Botond24/game_console/src/game/include/game.h

#ifndef GAME_H
#define GAME_H

#include <stdint.h>
#include <stdbool.h>

struct KeyState {
    bool up;
    bool down;
    bool left;
    bool right;
    bool a;
    bool b;
};

struct HAL {
    void (*draw_pixel)(int x, int y, uint16_t color);
    void (*clear_screen)(void);
    void (*render)(void);
    KeyState (*read_input)(void);
    void (*delay_ms)(uint32_t ms);
    int screen_width;
    int screen_height;
};

#endif
