Botond24/game_console/bootloader/src/periphs/oled.cpp

// IMPORTANT: MAKE SURE TO WRAP YOUR CODE IN MUTEXES
// IF UR ACCESSING THE OLED
#include "oled.h"
#include "pins.h"
#include <Adafruit_GFX.h>
#include <Adafruit_SSD1306.h>
#include <Wire.h>

#define WIDTH 128
#define HEIGHT 64
#define OLED_I2C_ADDR 0x3C

Oled::Oled() : display(WIDTH, HEIGHT, &Wire, -1) {}

const unsigned char chippy[] PROGMEM = {
    0x00, 0x00, 0x00, 0x00, 0xff, 0xff, 0xff, 0xff, 0xff, 0xff, 0xff, 0xff,
    0x00, 0x00, 0x00, 0x00, 0x00, 0x00, 0x00, 0x01, 0xc0, 0x00, 0x00, 0x00,
    0x00, 0x00, 0x00, 0x03, 0x80, 0x00, 0x00, 0x00, 0x00, 0x00, 0x00, 0x02,
    0x00, 0x00, 0x00, 0x00, 0x00, 0x00, 0x00, 0x00, 0xc0, 0x00, 0x00, 0x00,
    0x00, 0x00, 0x00, 0x04, 0x00, 0x00, 0x00, 0x00, 0x00, 0x00, 0x00, 0x00,
    0x20, 0x00, 0x00, 0x00, 0x00, 0x00, 0x00, 0x0c, 0x00, 0x00, 0x00, 0x00,
    0x00, 0x00, 0x00, 0x00, 0x30, 0x00, 0x00, 0x00, 0x00, 0x00, 0x00, 0x08,
    0x00, 0x00, 0x00, 0x00, 0x00, 0x00, 0x00, 0x00, 0x10, 0x00, 0x00, 0x00,
    0x00, 0x00, 0x00, 0x08, 0x00, 0x00, 0x00, 0x00, 0x00, 0x00, 0x00, 0x00,
    0x10, 0x00, 0x00, 0x00, 0x00, 0x00, 0x00, 0x08, 0x00, 0x00, 0x00, 0x00,
    0x00, 0x00, 0x00, 0x00, 0x10, 0x00, 0x00, 0x00, 0x00, 0x00, 0x00, 0x08,
    0x00, 0x00, 0x00, 0x00, 0x00, 0x00, 0x00, 0x00, 0x10, 0x00, 0x00, 0x00,
    0x00, 0x00, 0x00, 0x08, 0x00, 0x00, 0x00, 0x00, 0x00, 0x00, 0x00, 0x00,
    0x10, 0x00, 0x00, 0x00, 0x00, 0x00, 0x00, 0x08, 0x00, 0x00, 0x00, 0x00,
    0x00, 0x00, 0x00, 0x00, 0x10, 0x00, 0x00, 0x00, 0x00, 0x00, 0x00, 0x08,
    0x00, 0x00, 0x00, 0x00, 0x00, 0x00, 0x00, 0x00, 0x10, 0x00, 0x00, 0x00,
    0x00, 0x00, 0x00, 0x08, 0x00, 0x00, 0x00, 0x00, 0x00, 0x00, 0x00, 0x00,
    0x10, 0x00, 0x00, 0x00, 0x00, 0x00, 0x00, 0x08, 0x00, 0x00, 0x00, 0x00,
    0x00, 0x00, 0x00, 0x00, 0x10, 0x00, 0x00, 0x00, 0x00, 0x00, 0x00, 0x08,
    0x00, 0x00, 0x00, 0x00, 0x00, 0x00, 0x00, 0x00, 0x10, 0x00, 0x00, 0x00,
    0x00, 0x00, 0x00, 0x08, 0x00, 0x00, 0x00, 0x00, 0x00, 0x00, 0x00, 0x00,
    0x10, 0x00, 0x00, 0x00, 0x00, 0x00, 0x00, 0x08, 0x00, 0x00, 0x00, 0x00,
    0x00, 0x00, 0x00, 0x00, 0x10, 0x00, 0x00, 0x00, 0x00, 0x00, 0x00, 0x08,
    0x00, 0x00, 0x00, 0x00, 0x00, 0x00, 0x00, 0x00, 0x10, 0x00, 0x00, 0x00,
    0x00, 0x00, 0x00, 0x08, 0x00, 0x3f, 0x80, 0x00, 0x00, 0x03, 0xf8, 0x00,
    0x10, 0x00, 0x00, 0x00, 0x00, 0x00, 0x00, 0x08, 0x00, 0xff, 0x80, 0x00,
    0x00, 0x07, 0xf8, 0x00, 0x10, 0x00, 0x00, 0x00, 0x00, 0x00, 0x00, 0x08,
    0x01, 0xff, 0x80, 0x00, 0x00, 0x0f, 0xf0, 0x00, 0x10, 0x00, 0x00, 0x00,
    0x00, 0x00, 0x00, 0x08, 0x03, 0xff, 0x80, 0x00, 0x00, 0x1f, 0xf0, 0x00,
    0x10, 0x00, 0x00, 0x00, 0x00, 0x00, 0x00, 0x08, 0x03, 0xff, 0x80, 0x00,
    0x00, 0x3f, 0xf8, 0x00, 0x10, 0x00, 0x00, 0x00, 0x00, 0x00, 0x00, 0x08,
    0x03, 0xff, 0xe8, 0x00, 0x00, 0x3f, 0xff, 0xc0, 0x10, 0x00, 0x00, 0x00,
    0x00, 0x00, 0x00, 0x08, 0x07, 0xff, 0xf8, 0x00, 0x00, 0x3f, 0xff, 0xc0,
    0x10, 0x00, 0x00, 0x00, 0x00, 0x00, 0x00, 0x08, 0x07, 0xff, 0xf8, 0x00,
    0x00, 0x3f, 0xff, 0xc0, 0x10, 0x00, 0x00, 0x00, 0x00, 0x00, 0x00, 0x08,
    0x07, 0xff, 0xf8, 0x00, 0x00, 0x3f, 0xff, 0xc0, 0x10, 0x00, 0x00, 0x00,
    0x00, 0x00, 0x00, 0x08, 0x03, 0xff, 0xf8, 0x00, 0x00, 0x3f, 0xff, 0xc0,
    0x10, 0x00, 0x00, 0x00, 0x00, 0x00, 0x00, 0x08, 0x03, 0xff, 0xf8, 0x00,
    0x00, 0x3f, 0xff, 0x80, 0x10, 0x00, 0x00, 0x00, 0x00, 0x00, 0x00, 0x08,
    0x00, 0x00, 0x00, 0x00, 0x00, 0x00, 0x00, 0x00, 0x10, 0x00, 0x00, 0x00,
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

bool Oled::init() {
    mutex_init(&mutex);  // must be first
    Wire.setSDA(PIN_OLED_SDA);
    Wire.setSCL(PIN_OLED_SCL);
    Wire.begin();
    if (!display.begin(SSD1306_SWITCHCAPVCC, OLED_I2C_ADDR)) {
        Serial.println("[OLED] FAIL - SSD1306 not found");
        return false;
    }
    display.setTextSize(1);
    display.setTextColor(SSD1306_WHITE);
    display.setCursor(0, 0);
    return true;
}

void Oled::drawPixel(int x, int y, uint16_t whiteness) {
    lock();
    display.drawPixel(x, y, whiteness);
    unlock();
}


void Oled::flush() {
    lock();
    display.display();
    unlock();
}

void Oled::clear() {
    lock();
    display.clearDisplay();
    display.setCursor(0, 0);
    unlock();
}

void Oled::render() {
    lock();
    display.display();
    unlock();
}

void Oled::showImage(bool show) {
    lock();
    display.clearDisplay();
    if (show) display.drawBitmap(0, 0, chippy, 128, 64, SSD1306_WHITE);
    display.display();
    unlock();
}

size_t Oled::write(uint8_t byte) {
    lock();
    display.write(byte);
    unlock();
    return 1;
}

size_t Oled::print(const String& msg) {
    lock();
    display.print(msg);
    unlock();
    return msg.length();
}

size_t Oled::println(const String& msg) {
    lock();
    display.println(msg);
    unlock();
    return msg.length() + 1;
}
